dairyking98/Type-Elements/v4/site/accessories.md

---
layout: page
title: Accessories
---

Non-parametric companion parts that print alongside a machine's type
elements but aren't generated by this pipeline - no `config/`/`lib/`
counterpart, just a checked-in model plus a writeup. New accessories
land here as they're added.

- **[Mignon Index Holder](accessories/mignon_index_holder)** - holds
  the printed-out legend card alongside the printed Mignon element.
