dairyking98/Type-Elements/v4/site/assets/thumbnails/blickensderfer.png

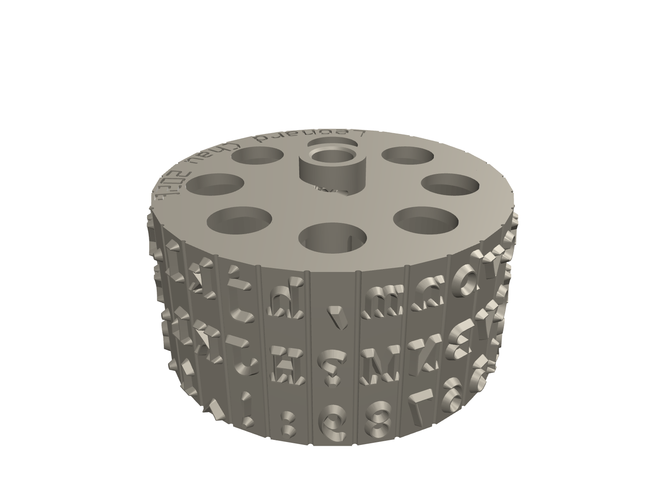
v4/site/assets/thumbnails/blickensderfer.png
