dairyking98/Type-Elements/v4/site/assets/thumbnails/glyph_A_minkowski.png

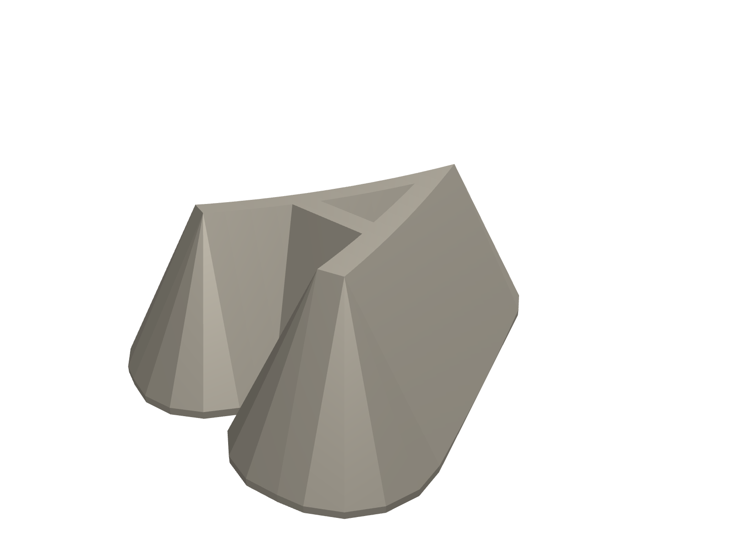
v4/site/assets/thumbnails/glyph_A_minkowski.png
