dairyking98/Type-Elements/v4/site/assets/thumbnails/glyph_A_no_minkowski.png

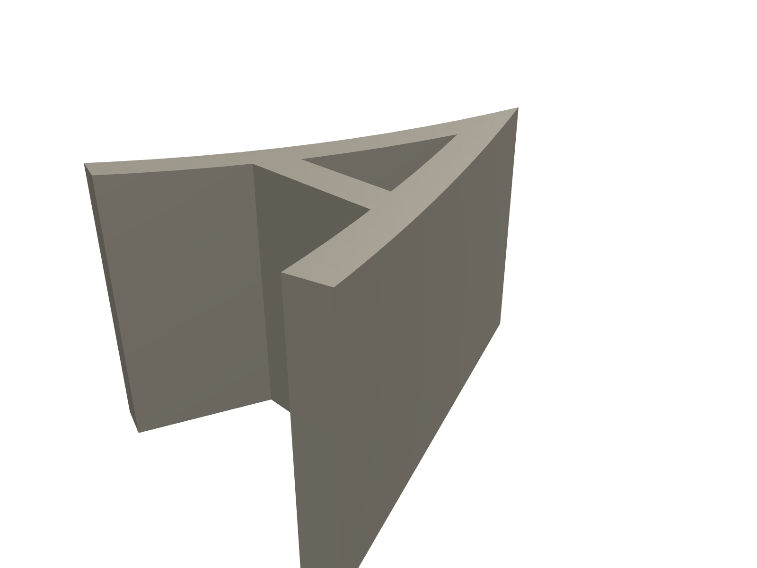
v4/site/assets/thumbnails/glyph_A_no_minkowski.png
