dairyking98/Type-Elements/v4/site/assets/thumbnails/hammond-shuttle.png

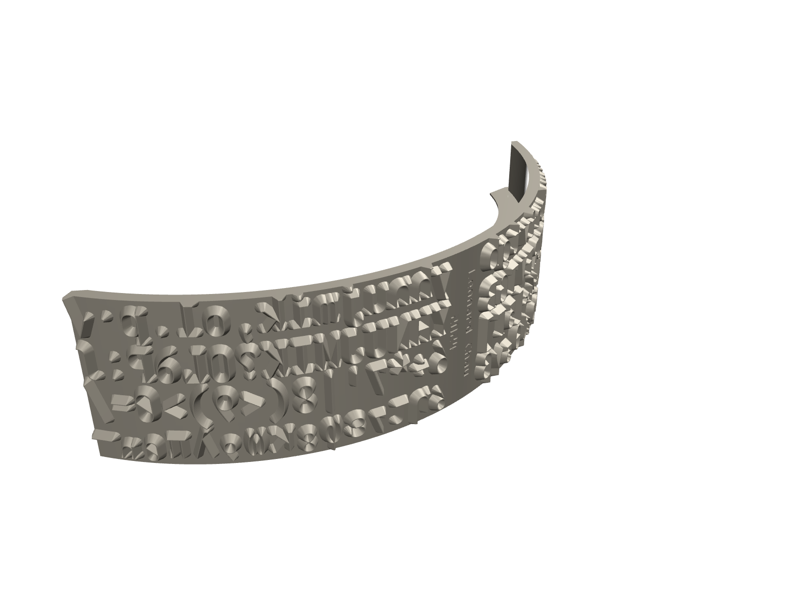
v4/site/assets/thumbnails/hammond-shuttle.png
