dairyking98/Type-Elements/v4/site/assets/thumbnails/helios-klimax.png

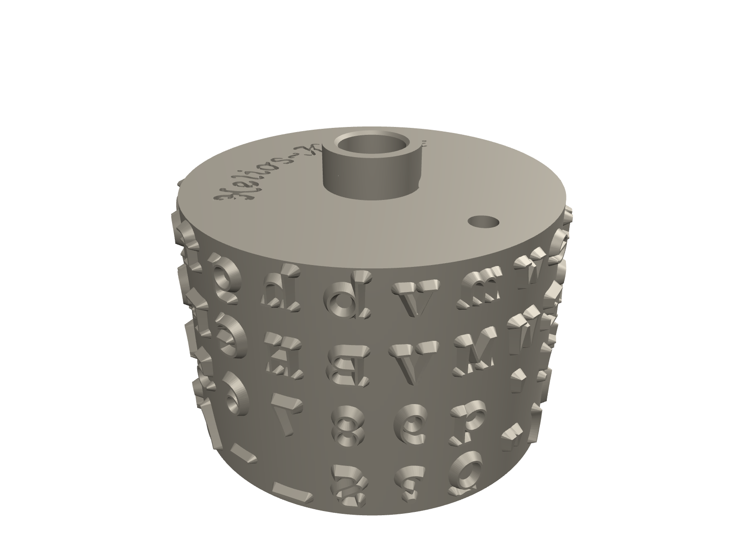
v4/site/assets/thumbnails/helios-klimax.png
