dairyking98/Type-Elements/v4/site/assets/thumbnails/mignon.png

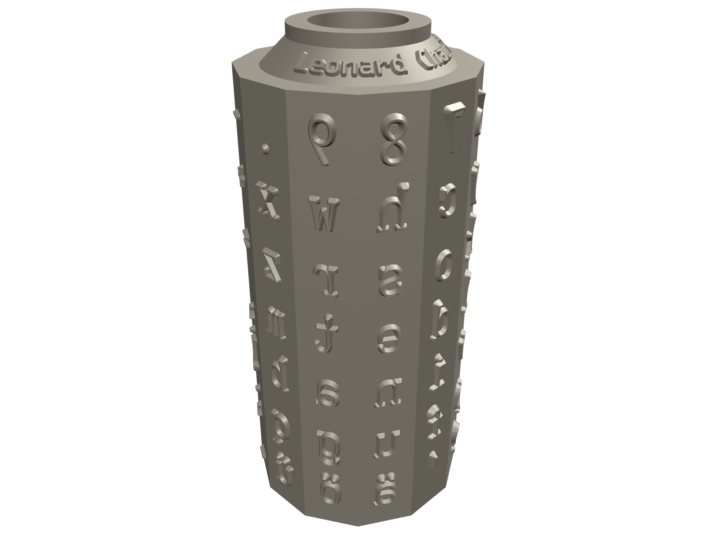
v4/site/assets/thumbnails/mignon.png
