dairyking98/Type-Elements/v4/site/assets/thumbnails/mignon_index_holder.png

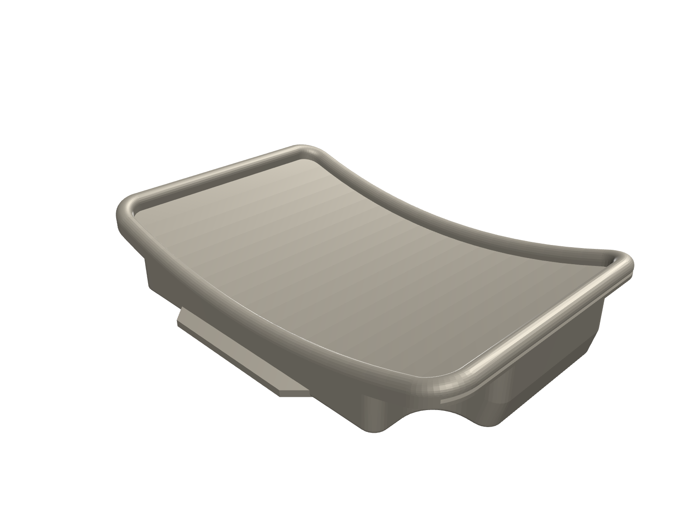
v4/site/assets/thumbnails/mignon_index_holder.png
