dairyking98/Type-Elements/v4/site/assets/thumbnails/oliver-slug.png

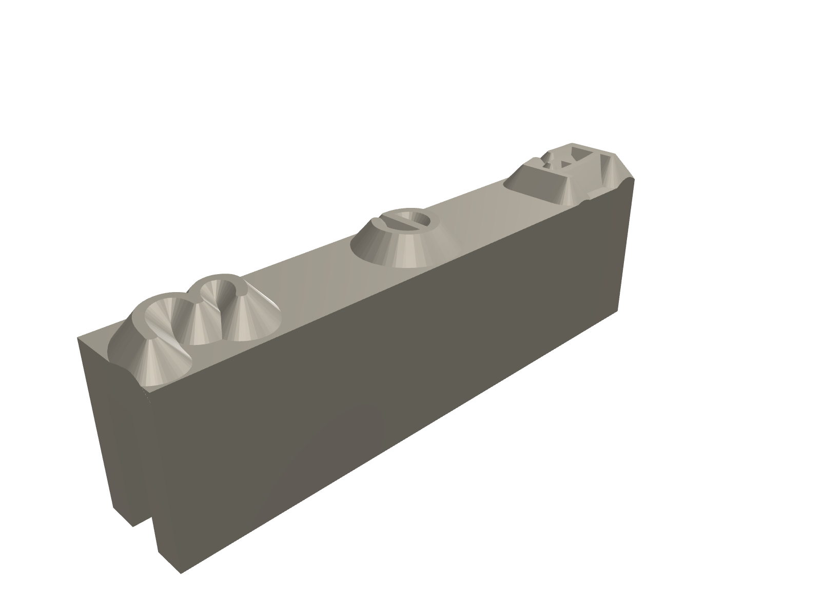
v4/site/assets/thumbnails/oliver-slug.png
