dairyking98/Type-Elements/v4/site/assets/thumbnails/postal.png

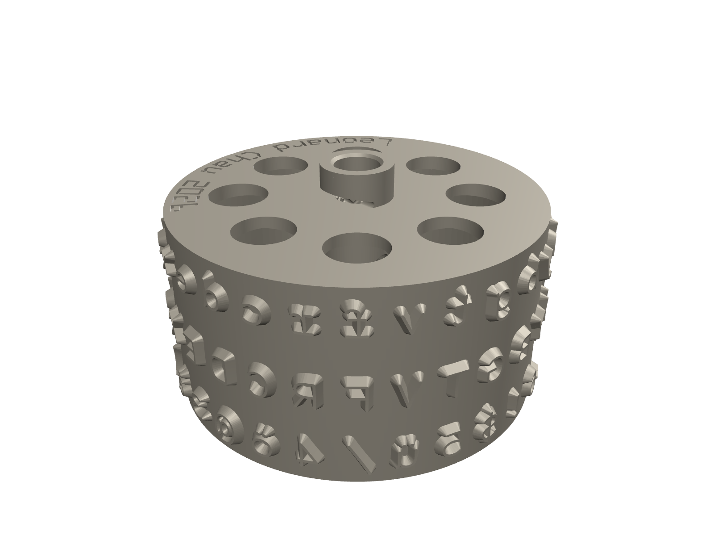
v4/site/assets/thumbnails/postal.png
