dairyking98/Type-Elements/v4/site/assets/thumbnails/resin_support_renders/blickensderfer_supports.png

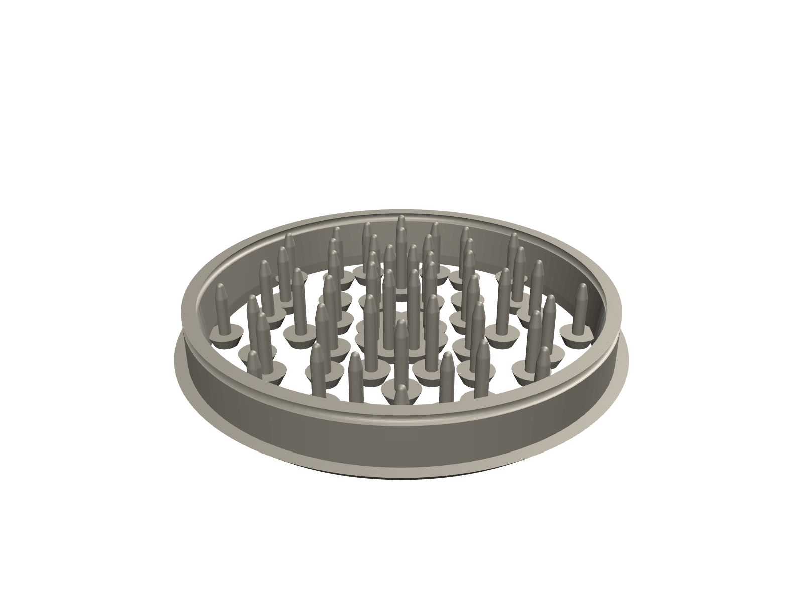
v4/site/assets/thumbnails/resin_support_renders/blickensderfer_supports.png
