dairyking98/Type-Elements/v4/site/assets/thumbnails/selectric-composer.png

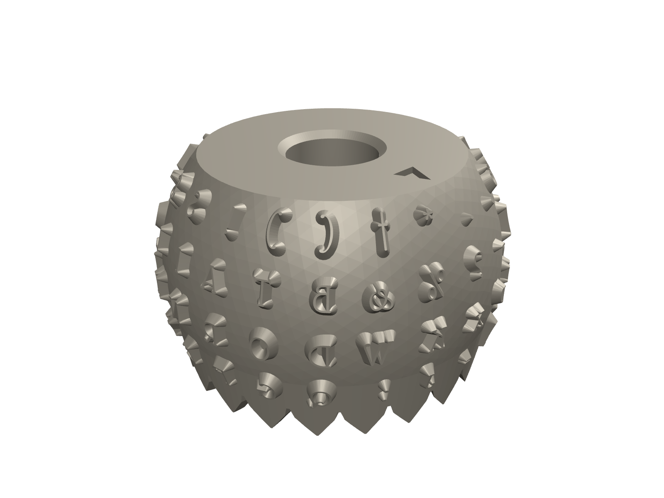
v4/site/assets/thumbnails/selectric-composer.png
