dairyking98/Type-Elements/v4/site/assets/thumbnails/type-slug.png

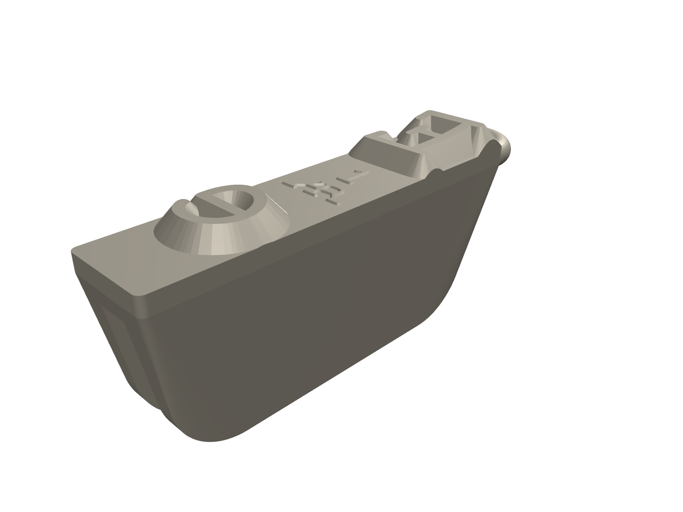
v4/site/assets/thumbnails/type-slug.png
