dairyking98/Type-Elements/v4/site/assets/thumbnails/vogue-slug.png

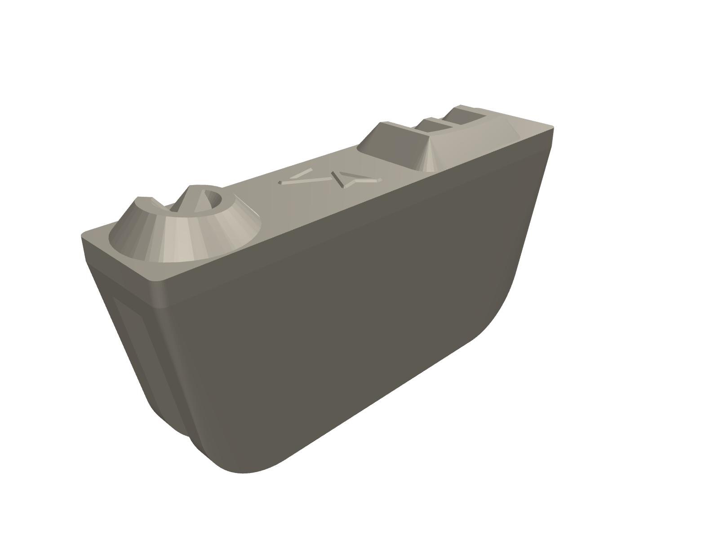
v4/site/assets/thumbnails/vogue-slug.png
