dairyking98/Type-Elements/v4/example_renders/helios-klimax.stl

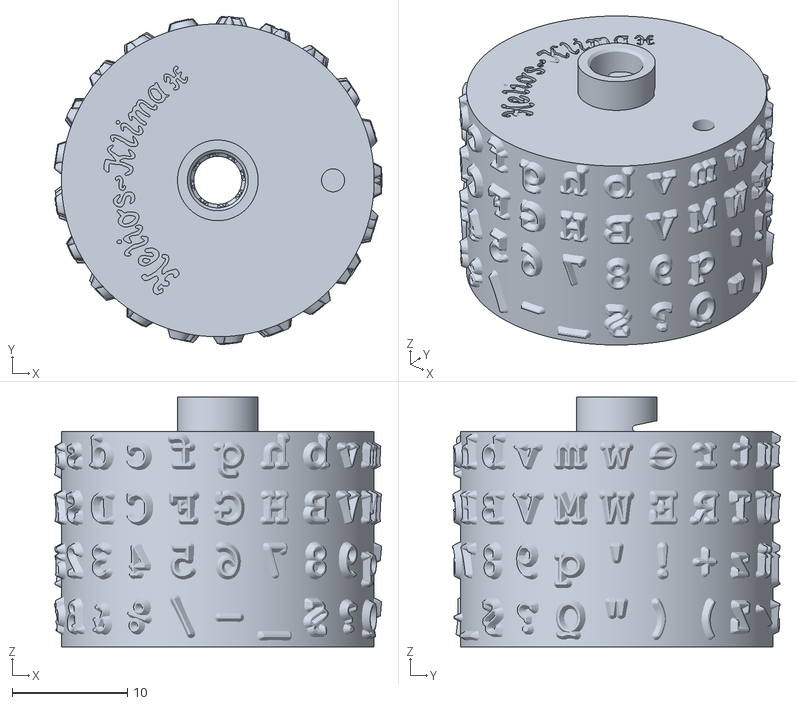
[picture p33: CAD file, 2026-08-02]
v4/example_renders/helios-klimax.stl
28.4 x 28.5 x 21.7
