dairyking98/Type-Elements/v4/example_renders/oliver-slug.stl

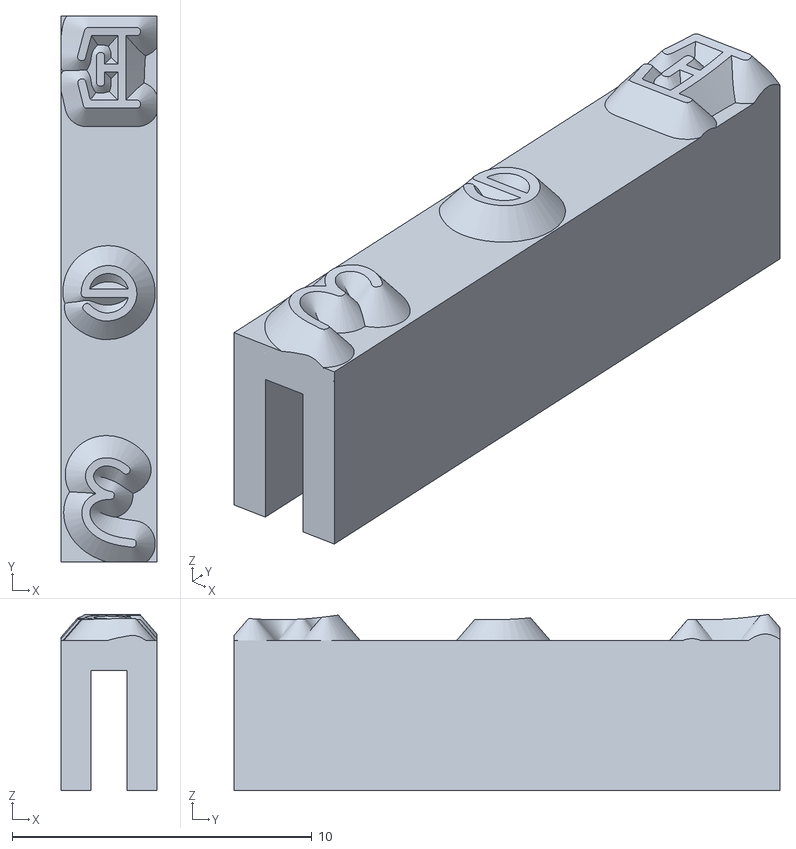
[picture p34: CAD file, 2026-08-02]
v4/example_renders/oliver-slug.stl
3.20 x 18.2 x 5.88
