dairyking98/Type-Elements/v4/example_renders/mignon.stl

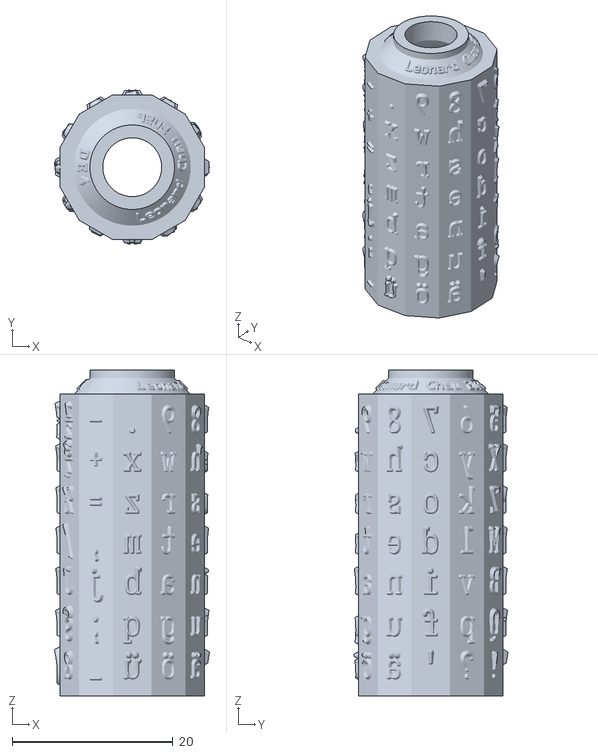
[picture p35: CAD file, 2026-08-02]
v4/example_renders/mignon.stl
19.3 x 19.2 x 40.5
