dairyking98/Type-Elements/v4/example_renders/postal.stl

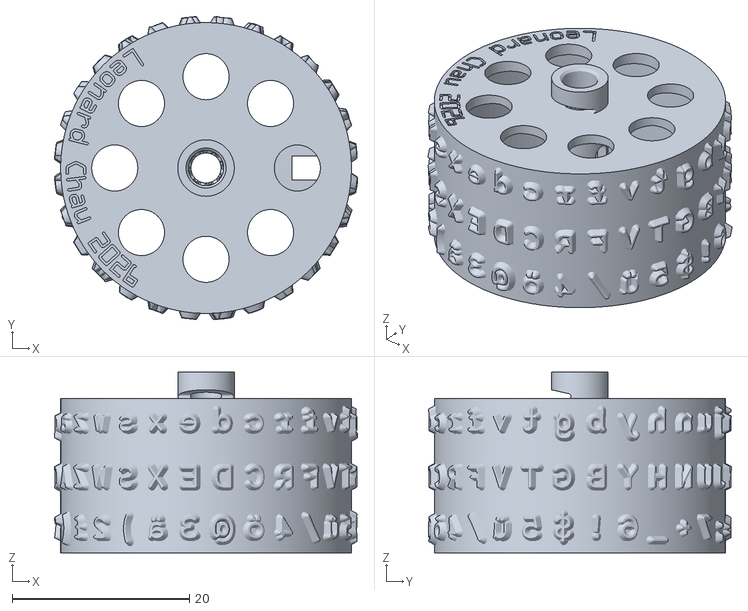
[picture p36: CAD file, 2026-08-02]
v4/example_renders/postal.stl
34.2 x 34.2 x 20.4
