dairyking98/Type-Elements/v4/example_renders/bennett.stl

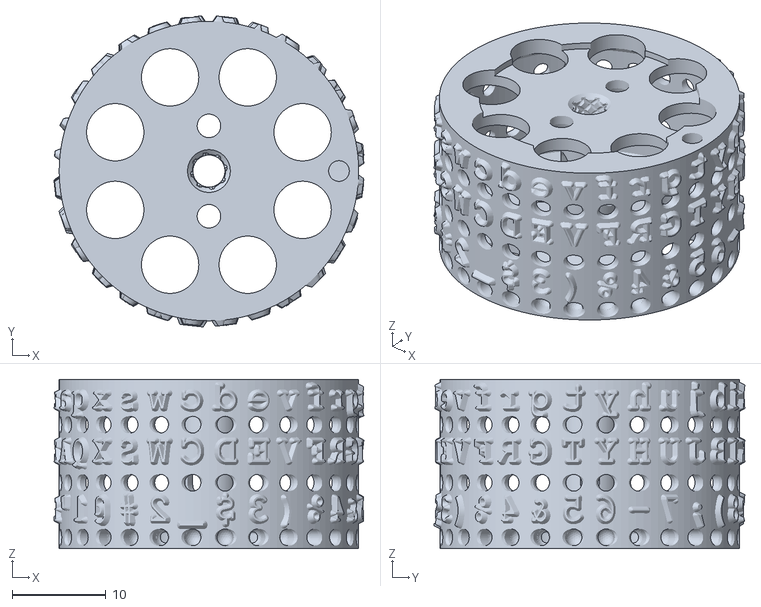
[picture p37: CAD file, 2026-08-02]
v4/example_renders/bennett.stl
33.0 x 33.1 x 18.0
