dairyking98/Type-Elements/v4/config/hammond.yaml

# Hammond type shuttle - real parameters ported from v2/hammond.scad (see
# that file's header comment for the full v2-internal glyph-pipeline
# unification derivation this config's layout/element section relies on).
#
# Hammond shares the glyph placement pipeline (place_on_cylinder/TextRing/
# CalibrationTextRing via cylinder_machine.py, plus cylinder_machine.
# _resin_rod() for the individual resin-support rod shape) with
# Blickensderfer/Postal/Mignon/Bennett/Helios, confirmed by v2/hammond.scad's
# own header comment: its arc-placement Theta formula was verified
# algebraically to reduce exactly to the shared lib's (Angle_Half_Step+
# latitude)*Latitude_Int, by treating the shuttle arc as a "fake cylinder"
# of diameter 2*Shuttle_Arc_Radius. Despite that, Hammond is NOT a
# cylinder-family body: it strikes a flat anvil (no curved platen - see
# platen_diameter below) and its body geometry (ShuttleCylinder/AnvilShape/
# Rib/PinSupport/ShuttleTaper/Label) shares nothing with cylinder_machine.py
# - see lib/hammond.py's module docstring for the full comparison.
#
# hammond_split.scad (a completely different two-piece spoke/folder
# assembly, self-contained with its own inlined glyph placement - see
# SESSION_LOG.md's Hammond audit chapter) is a SEPARATE machine in
# everything but name and is NOT covered by this config or lib/hammond.py -
# deferred to its own future port.
#
# Groove=true (v2/hammond.scad:258's alternate snap-fit/groove assembly
# variant, GroovedShuttle()/Groove()/PinSupport2()) is likewise deferred -
# Groove=false (the default) is the only variant ResinPrint's real dispatch
# path (VertResinPrint2->RibbedShuttle) exercises, so it's the one ported
# here. Cutout_Test/Cutout_Test_Array/Show_Align_Bounds (preview-only
# debug toggles, already dead/unused per v2's own comments at lines 110-113)
# are not ported, matching how other machines drop confirmed-dead v2
# customizer params.
#
# Default layout is Normal_U (LAYOUTS[0] in v2/lib/layouts/hammond_layouts.
# scad, 3 rows x 30 columns, Layout_Selection=0's default) - Hammond's other
# 7 named presets (Normal Ideal/Universal, Math/DVORAK/DHIATENSOR/Comic Mono/
# Glagolitic/Attic) are real alternate v2 presets, not yet wired into
# tune.py's named-preset picker (see SESSION_LOG.md).
#
# Typeface_2/Type_2_Size/Typeface_2_Chars (v2:167-169 - Hammond's
# always-on Glagolitic secondary-typeface tier, GalFont/GalFontSize/GalChars
# renamed) is NOT ported: it only ever matches characters that appear in
# the Glagolitic layout preset (LAYOUTS[6]), which isn't the default here -
# confirmed dead for every other layout, same treatment as bennett.yaml's
# dead-param callouts. Revisit if/when the Glagolitic preset is wired up.
# Font_Weight_Offset/X_Font_Weight_Adj/Y_Font_Weight_Adj (v2:149-151) are
# also 0/no-op in the real machine and not ported for the same reason.

machine: hammond

font:
  # v2's real value is the font family name "Iosevka Fixed Slab"
  # (Font_Size=3.10) - not installed here; nearest real file on disk.
  path: "/home/lchau/fonts/Library/Typewriter & Monospace/Iosevka Term Slab.ttf"
  size_mm: 3.10

label:
  # v2's real value is "OCR\\-A II" (a real installed font here, unlike
  # Bennett's substitution).
  font_path: "/home/lchau/fonts/Library/Typewriter & Monospace/OCR-A II Regular.ttf"
  label1: "Leonard Chau"   # Shuttle_Label1
  label2: "2024"           # Shuttle_Label2
  label_size_mm: 1.3       # Shuttle_Label_Size
  depth_mm: 0.2            # Shuttle_Label_Depth

# Real machine dimensions, v2/hammond.scad:198-262 - "shuttle" here is the
# arc-shaped print body (Anvil_OD/Shuttle_Arc_Radius is the fake-cylinder
# Element_Diameter the glyph pipeline wraps text onto; Anvil_ID is the
# printer's real anvil bore the shuttle clips around).
# Secondary font - characters listed in font2_chars are struck in this
# font/size instead of the main one. Same feature the Selectric family and
# Hammond Split have, under the same key names. Empty font2_chars =
# inactive (the default), so this changes nothing until it is filled in.
# The real use is glyph coverage: measured across the 170 distinct
# characters in all 28 Blickensderfer layout presets, Royal Vogue v3 is
# missing 87 (fractions, currency), Erica Type 52 (including "@"), Alma
# Mono and CMU Typewriter 50 each, and no non-Hebrew font covers the
# Hebrew-English preset at all.
font2:
  font2_path: ""            # blank = use the main font
  font2_size_mm: 0.0        # 0 = use the main font size
  font2_chars: ""

element:
  shrinkage_multiplier: 1.00       # Shuttle_Arc_Radius_Shrinkage_Multiplier
  anvil_od: 73.15                  # Element_Diameter = anvil_od*shrinkage_multiplier
  anvil_id_raw: 66.0
  shuttle_thickness: 1.36          # also Letter_Placement_Protrusion (v2:380)
  # v2's Shuttle_Text_Protrusion (0.9) is not carried as its own key:
  # protrusion is expressed fleet-wide as element.min_final_character_
  # diameter below, from which it is derived. Dropped rather than left as a
  # second spelling that could silently disagree.
  # Diameter across two opposing character tips - the fleet-wide way of
  # expressing protrusion (same key the cylinder machines use). The shuttle
  # surface is element_diameter + 2*shuttle_thickness = 75.87, so this is
  # 0.9mm of relief. No minimum-vs-maximum here: a flat anvil, no platen
  # scallop to vary it.
  min_final_character_diameter: 77.67
  normal_shuttle_height: 13.6
  math_shuttle_height: 18.24
  shuttle_height_offset: 3
  shuttle_rib_plane_base: 6.7      # Shuttle_Rib_Plane = this + shuttle_height_offset
  shuttle_rib_thickness: 0.24
  shuttle_rib_width: 2.9
  shuttle_square_hole_offset: 6.4
  shuttle_square_hole_width: 2.67
  shuttle_square_hole_length: 1.60
  shuttle_square_hole_radius: 0.4
  shuttle_pin_support_height: 1.5
  shuttle_pin_support_base_width: 6
  shuttle_pin_support_base_length: 7.8
  shuttle_pin_support_height_offset: 1.5
  # Shuttle_Pin_Support_Height2 (v2:236) - PinSupport2()'s own dimension
  # (that module is dead/unused - see element.groove's comment), but this
  # SAME value is also used by HorizResinSupport2's "under Pinhole" tier
  # (lib/hammond.py's HorizRibbedResinSupport()), so it's real/needed.
  shuttle_pin_support_height2: 2.0
  shuttle_rib_hump_distance: 9
  shuttle_rib_circle: 159
  shuttle_rib_circle_radius: 19
  shuttle_taper_deg: 2
  shuttle_taper_step: 0.5
  # Angle_Pitch = (angular_span_deg/angular_divisions)/shrinkage_multiplier
  # (v2:203) - the shuttle's real physical arc spans 120 degrees over 32
  # divisions; Latitude_Int (the glyph pipeline's column-to-angle step)
  # is this same value, not an independently-tunable one.
  angular_span_deg: 120
  angular_divisions: 32
  # Is_Math (v2:128 - search(LAYOUTS[Layout_Selection][3],"Math")) is
  # DERIVED in lib/hammond.py's configure() from len(layout.rows)==4 (the
  # Universal, Math preset is the only real 4-row layout - see tune.py's
  # Layout tab) - not a separate settable toggle here, so it can't drift
  # out of sync with which preset is actually selected.
  # Rib()'s fillet region insets its resin-support-clearance corner by this
  # much (v2:351 "Cp_1_X=Shuttle_Arc_Radius*cos(Theta_A)-2  //limit of resin
  # support" - a real, named machine clearance, not a construction sentinel).
  rib_fillet_resin_clearance: 2.0
  # Groove (v2:258) - the shuttle's two real, mutually-exclusive BODY
  # ASSEMBLY mechanisms: false (default) is the internal rib + square
  # drive-pin boss (Rib()/PinSupport()/PinSupportHole(), assembled
  # separately and glued/pinned to the shuttle body); true is a snap-fit
  # groove cut directly into the shell (Groove()/ResinChamfer(), no
  # separate rib piece at all) - see lib/hammond.py's GroovedShuttle()-
  # equivalent path for the full derivation. tune.py's Build tab shows
  # this as the "Rib" checkbox (inverted) - user-facing wording is
  # "Without Rib" for groove=true, to avoid confusion with the
  # UNRELATED resin.horizontal_method "Cut Groove" option below (a
  # resin-support scheme, not a body-assembly choice - the two used to
  # share the word "groove" with no way to tell them apart by name).
  # v2's PinSupport2()/Groove_Retaining_Pin_Diameter are declared but
  # never actually called/referenced anywhere in v2/hammond.scad -
  # confirmed dead code, not ported (same convention as bennett.yaml's
  # dead-param callouts).
  groove: false
  shuttle_groove_nub_angle: 29           # Shuttle_Groove_Nub_Angle (deg)
  groove_tab_width: 3.15                 # Groove_Tab_Width (3+.15 in v2)
  groove_opening_offset: 0.5             # Groove_Opening_Offset
  support_groove_thickness: 0.5          # Support_Groove_Thickness - also
                                          # derives Support_Groove_R, used by
                                          # resin.horizontal_method's Cut
                                          # Groove ring (v2:322 also uses it
                                          # for ResinChamfer(), currently
                                          # disabled - see lib/hammond.py's
                                          # Additive())
  # v4-specific, not a v2 value - FDM print-fit clearance for the "Rib"
  # Build target's groove-interface flange (RibOnly(), see its own
  # docstring and GrooveShape()'s "shrink" parameter). Shrinks the
  # flange (printed as its own separate FDM part, meant to snap into a
  # "Shuttle" (groove=true) body's cut slot) rather than growing the
  # Shuttle's own groove cut - typical FDM practice, printers tend to
  # oversize solid protrusions more than they undersize cut features.
  # 0.15mm is a reasonable starting point for a snug slide-fit at
  # typical 0.4mm-nozzle FDM tolerances - tune per printer/filament.
  rib_interface_offset_mm: 0.15
  # v4-specific, not a v2 value - extra radius added to the Rib flange's
  # 4 nub-clearance cutouts (see GrooveShape()'s nub_grow parameter),
  # independent of rib_interface_offset_mm - gives the flange's own
  # clearance holes some FDM-fit margin over the Shuttle-side nub
  # geometry. Only affects RibOnly(), never the Shuttle-side cutter.
  rib_nub_growth_mm: 0.15
  # v4-specific, not a v2 value - how far the Rib flange's center tang
  # (the feature that plugs through the Shuttle's cut opening) reaches,
  # in absolute mm from the rotation axis. Deliberately OMITTED here -
  # lib/hammond.py's configure() defaults it to Shuttle_Arc_Radius+
  # Shuttle_Thickness (the Shuttle's own real outer wall radius) when
  # this key is absent, so the tang sits flush with the Shuttle's real
  # outer surface automatically, tracking those two values instead of a
  # separately-maintained literal that could drift out of sync with
  # them. Only add this key (see lib/hammond.py's Rib_Tang_Length
  # comment) if a physical fit-check shows it should stop short of or
  # protrude past that surface.
  # rib_tang_length_mm: <override, mm from rotation axis - see comment above>
  # v4-specific, not a v2 value - RibOnly() only: when true, omits
  # PinSupport()'s "top" boss (keeps only "bottom"), so the printed part
  # has a protruding pin-boss feature on one Z side only and can sit
  # flat on the buildplate without needing supports under the other
  # side's overhang. Never applied to the fused Shuttle with Rib print.
  rib_flat_bottom: false

# quality/facet counts - v2:79-92. Surface_Fn mirrors Cyl_Fn (v2's own
# comment: "no separate structural-quality tier from Cyl_Fn").
quality:
  cyl_fn: 360
  surface_fn: 360
  minkowski_fn: 12                 # Mink_Fn
  # Wall banding. The body is pre-split into horizontal bands so the boolean
  # that unions the characters into it never has a full-height face to
  # shatter into long near-zero-area slivers. Bands are never made SHORTER
  # than this; 0 = auto, one band per angular facet width (bands roughly as
  # tall as they are wide). Raise it to coarsen an over-fine wall.
  min_band_height_mm: 0.0

# Baseline (v2:130) is [Lowercase, Uppercase, Figures, Math], measured from
# the bottom RIB plane (Baseline_Z_Offset=Rib_Bottom_Z, a derived value -
# see lib/hammond.py's configure()). This master config's default layout
# (Universal) has only 3 rows, so only the first 3 entries apply
# here - the real 4th (Math, -9.89) value lives in tune.py's
# LAYOUT_PRESET_BASELINE_ROW_BY_MACHINE["hammond"]["Universal, Math"],
# applied automatically when that layout preset is selected (switches
# baseline_row/cutout_row to 4 entries at the same time as rows, since
# Is_Math is derived from row count - see lib/hammond.py's configure()).
# Cutout (v2:133) is unused (Skip_Platen_Cutout=true, see lib/hammond.py)
# - cutout_row is set equal to baseline_row as a documented no-op rather
# than porting the dead [0,0,0,0].
#
# Placement_Map (v2:371, col<=14 ? col-16 : col-14) is Hammond's real
# non-identity physical-column mapping for the arc's seam at column 14/15 -
# materialized as literal data here (not computed from layout.rows' length
# at load time) matching how every other machine stores placement_map, per
# this repo's "pick one convention, don't let it re-fork per machine" rule
# - tune.py's Layout tab reads layout.placement_map/latitude_columns
# directly. latitude_columns must stay in sync with placement_map/rows -
# edit both together if you ever change layout.rows' column count.
layout:
  baseline_row: [3.74, -1.21, -5.71]
  # Cutout (v2:133) is unused - Skip_Platen_Cutout means the (y-offset)^2
  # scallop term is multiplied by platen_radius_mm=0 regardless of offset,
  # so cutout_row-baseline_row's value can't affect geometry. Set equal to
  # baseline_row (offset=0) as a documented no-op rather than porting the
  # dead v2 Cutout=[0,0,0,0] - stored literally (not derived at load time)
  # since tune.py's Element tab reads layout.cutout_row directly, same as
  # baseline_row.
  cutout_row: [3.74, -1.21, -5.71]
  latitude_columns: 30
  placement_map: [-16, -15, -14, -13, -12, -11, -10, -9, -8, -7, -6, -5, -4, -3, -2, 1, 2, 3, 4, 5, 6, 7, 8, 9, 10, 11, 12, 13, 14, 15]
  rows:
    - "-;p.lo,kimjunhybgtvfrcdexswzaq"
    - "!:P.LO?KIMJUNHYBGTVFRCDEXSWZAQ"
    - "/=0.)9°(8^'7*&6¢_5£%4+$3×#2@\"1"
  modify_glyphs: false

alignment:
  mode: "center"
  center_offset_mm: 0.0
  left_offset_mm: 0.0
  modified_left_chars: ""
  modified_left_offset_mm: 0.0
  modified_right_chars: ""
  modified_right_offset_mm: 0.0
  # Per-character baseline overrides, y-axis counterparts to the
  # modified_left/right_chars nudges above (see glyph_poc.alignment_offset).
  # caret_drop_mm shifts "^" DOWN - the Blickensderfer's caret sits on the
  # baseline, but digital fonts draw U+005E up at cap height because there
  # it doubles as the spacing circumflex accent. underscore_lift_mm shifts
  # "_" UP - many TTFs sink U+005F well below the baseline to clear
  # descenders in running text, which drops it out of the character cell on
  # a struck element. Both 0.0 = use the font's own glyph position, i.e. the
  # behavior every config had before these keys existed. Idea/problem
  # statement from RobertG's OpenSCAD Blickensderfer generator
  # (badonoer.blogspot.com, CC BY-SA 4.0) caretDrop/uScoreLift.
  caret_drop_mm: 0.0
  underscore_lift_mm: 0.0

# mesh-pipeline build settings (v4-specific, not real v2 numbers) - see
# config/bennett.yaml's matching comment. platen_diameter=0/no cutout
# (Skip_Platen_Cutout=true, v2:384 - Hammond strikes a flat anvil, not a
# curved platen) translates to platen_radius_mm=0 in build_glyph's
# scallop formula z=(y-offset)^2*platen_radius_mm - a real 0 makes the
# scallop term vanish for every y, i.e. a genuinely flat print face,
# rather than an undefined 1/0. See lib/hammond.py's configure().
build:
  flatness_tolerance_mm: 0.005
  pre_minkowski_char_height_mm: 1.0
  # MINKOWSKI CONE HEIGHT - the tapered part of the character, added BELOW
  # the straight part. Total character depth is pre_minkowski_char_height_mm +
  # this, and the tip does not move when either changes. Lower it for a
  # shallower flare without pulling the root out of the wall - which is
  # what shrinking the character alone used to do, until the roots lifted
  # clear and the characters floated free of the body.
  minkowski_cone_height_mm: 2.0
  # Trim each placed character to its own angular slot so its Minkowski
  # draft skirt cannot bleed into the neighbouring character. See
  # cylinder_machine._clip_to_cell. Off = the historical behavior.
  clip_to_cell: false
  resin_support: true               # Resin_Support (v2:298)
  target: "element"
  minkowski_enabled: false           # Mink_On default (v2:102)
  draft_angle_deg: 55.0              # Mink_Draft_Angle (v2:106)

# Resin support: individual rod SHAPE reuses cylinder_machine._resin_rod()
# (same shared primitive Mignon/Bennett already reuse - NOT Hammond's own
# v2 ResinRod()/RodTip() modules, which are custom one-off variants of the
# same idea). Placement is Hammond-specific (lib/hammond.py) since the
# arc-shaped body has no radial-wall/sloped-core topology for cylinder_
# machine.py's BottomSupports/SpeedHoleSupport/DrivePinSupport placement
# layer to apply to - v2/lib/resin_support.scad's own header explicitly
# excludes Hammond/IBM from that placement layer for this reason. The one
# genuinely new primitive is the angled reinforcement rod between adjacent
# support rods (gusseting) - sp.connecting_rod(), ported from v2's
# ConnectingRod() (v2/hammond.scad:419), which doesn't exist for any other
# machine since none of their resin-support systems brace rods against
# each other.
resin:
  resin_fn: 20
  rod_od: 0.9                       # Resin_Support_Rod_Thickness
  tip_od: 0.4                       # Resin_Support_Contact_Diameter
  tip_l: 1.0                        # RodTip()'s h=1 cylinder section
  inset: 0.2                        # tip_od/2, same convention as bennett.yaml
  min_rod_height: 2.0                # Resin_Support_Min_Height
  raft_thickness: 1.5                # Resin_Support_Base_Thickness
  raft_od: 1.6                       # 2*Resin_Support_Buildplate_Radius
  spacing: 3.0                      # Resin_Support_Spacing - real angular
                                     # rod pitch is spacing/Shuttle_Arc_Radius
                                     # radians (v2:615's thetaspacing formula)
  edge_gap: 0.1                     # Resin_Support_Edge_Gap (v2:314)
  tip_interference: 1.2             # Tip_Interference (v2:324) - ResinRod2()'s
                                     # real tip overlap-fit depth (horizontal,
                                     # non-grooved support only). NOT currently
                                     # consulted by lib/hammond.py's _rod2() -
                                     # v2's real value was calibrated against
                                     # ResinRod2's own hardcoded 2mm cone, which
                                     # doesn't match this port's substituted
                                     # resin_rod() shape (Resin_Tip_L=1.0mm) -
                                     # see _rod2()'s docstring. Kept as real,
                                     # documented v2 machine data, not deleted.
  # Resin_Support_Orientation (v2:300) - "vertical" stands the shuttle up
  # on one end (v2's VertResinPrint2, rotate([0,-90,0])) and reuses v2's
  # real VertResinSupport2() placement math (lib/hammond.py's
  # ResinSupport()). "horizontal" prints it flat in its natural as-built
  # frame, outer-wall support scheme picked by horizontal_method below.
  orientation: vertical              # [vertical, horizontal]
  # horizontal_method - v4-specific, NOT a direct v2 customizer field
  # (v2:1060-1073's real ResinPrint() dispatcher only ever wires up
  # HorizGroovedResin3 for Resin_Support_Orientation==1 - HorizResinPrint2/
  # HorizResinSupport2, the rod scheme, are real complete v2 functions but
  # never called from there; see lib/hammond.py's ResinPrint() docstring
  # for the full derivation of why both are ported and exposed anyway).
  # Picks which OUTER-WALL horizontal support scheme is used, independent
  # of element.groove/the Build tab's Rib checkbox: "cut_groove" is
  # HorizGroovedResin3's swept perforated breakaway-groove ring
  # (HorizGroovedResinSupport()); "resin_rod" is HorizResinPrint2/
  # HorizResinSupport2's real per-rod scheme for the outer wall
  # (HorizWallRodSupport()). v2:1006-1021/864-950 respectively - both
  # real, faithfully-ported v2 schemes, not a simplified stand-in.
  # Independent of body assembly because the ring only spans the outer
  # wall band (r0..r0+Shuttle_Thickness) and never touches the rib
  # feature either way - but whenever the body actually HAS a rib
  # (element.groove=false), the rib's own back-plane/pin-hole area still
  # always needs its own resin-rod supports regardless of this setting
  # (HorizRibResinSupport() - there's no cut-groove equivalent for that
  # geometry), added on top of whichever outer-wall method is chosen here.
  horizontal_method: resin_rod       # [cut_groove, resin_rod]

output:
  directory: "output"
  stl_name: "hammond_running.stl"

# tune.py's Type Test tab (v4-specific) - see config/bennett.yaml's
# matching comment.
type_test:
  cpi: 10.0                         # Test_CPI
  lpi: 6.0
  text: |-
    The quick brown fox jumps over the lazy dog 1234567890

# Calibration - v2 has no Cutout_Test/Baseline_Test defaults active
# (Cutout_Test=false at v2:110, Baseline_Test=false at v2:115), same as
# Bennett's real defaults.
calibration:
  test_char: "H"
  vary_baseline: false
  vary_cutout: false
  start: -0.7
  interval: 0.05

# The flat 2D "index" reference card - v1/Hammond/HammondIndex.scad
# ported to lib/hammond_legend.py (SVG output via generate_legend.py,
# entirely separate from the 3D element build above - see that module's
# docstring). Every number below is v1's real customizer default
# (HammondIndex.scad line cited), not invented. Displays layout.rows
# above as a conventional QWERTY-style 3-row x 10-column reference,
# reading the real 30-key shuttle arc.
legend:
  # Real per-row hand-measured spans against an actual original card
  # (2026-08-06), replacing v1's own taper-formula-derived approximation
  # (v1 QP_Length=178/ZExclamation_Length=200.4, no separate A-to-:
  # measurement at all - see lib/hammond_legend.py module docstring's
  # divergence note). qp_length_mm's value happens to be unchanged from
  # v1's own (178.0mm) - real coincidence, not copied verbatim.
  qp_length_mm: 178.0                 # Q key to P key, top row
  a_colon_length_mm: 188.0            # A key to : key, middle row
  z_exclamation_length_mm: 198.0      # Z key to ! key, bottom row
  # Row-to-row vertical pitch (both Q<->A and A<->Z gaps) and the
  # absolute anchors - see lib/hammond_legend.py's _locate() docstring.
  row_separation_mm: 18.45
  left_margin_mm: 38.0                # shared start x for all 3 rows (Q/A/Z vertically aligned)
  bottom_margin_mm: 9.2                # card bottom edge to the Z row
  # Real fixed cut size - not derived from content bounds (this card's
  # margins are genuinely asymmetric top/bottom). Width = left_margin_mm
  # + z_exclamation_length_mm (the widest row) + a matching 38mm right
  # margin = 274.0mm exactly.
  card_width_mm: 274.0
  card_height_mm: 60.0
  card_corner_radius_mm: 19.0         # top two corners only - see _card_border()
  # The rounding circle's own center height (not derived as card_height_mm
  # - card_corner_radius_mm - a real independent measurement). 38+19=57mm
  # falls short of card_height_mm (60mm), so the arc needs a straight
  # vertical bridge up to the top edge - see _card_border()'s docstring.
  card_corner_center_y_mm: 38.0
  card_border_stroke_mm: 0.1          # SVG stroke width for the cut-outline path (visual only, not a cut parameter)
  circle_id_mm: 14.0                  # v1 Circle_ID (:60)
  circle_thickness_mm: 0.5            # v1 Circle_Thickness (:61)
  cap_size_mm: 6.0                    # v1 CAP_Size (:54)
  fig_size_mm: 4.0                    # v1 FIG_Size (:56) - also reused for the lowercase/punctuation label (v1 does the same, :135/181)
  capfig_mod_size_mm: 4.0             # v1 CAPFIG_ModSize (:58)
  fig_offset_mm: 2.5                  # v1 FIG_Offset (:40)
  lowercase_offset_mm: -5.5           # v1 Lowercase_Offset (:42)
  cap_offset_mm: -4.5                 # v1 CAP_Offset (:44)
  fig_dupe_offset_mm: 3.0             # v1 FIG_Dupe_Offset (:46)
  capfig_offset_mm: -1.5              # v1 CAPFIG_Offset (:48)
  capfig_mod_chars: "!:?-\"&"         # v1 CAPFIG_Mod (:21)
  # v1 Lowercase_Mod (:23) - minus the literal "☺" (a real character in
  # v1's string, but not a meaningful key on any of this config's real
  # layout.rows), PLUS "-" - v1's own real Layout[0][0]="-" (a genuine
  # standalone character, not the lowercase form of its own key's CAP
  # letter, "!") is missing from v1's own Lowercase_Mod (confirmed: a
  # real openscad-nightly render of the actual v1 file shows the same
  # gap - no dash anywhere), so the dash never gets drawn in v1's real
  # output either. Added here as a deliberate fix rather than
  # reproducing that gap - a legend that silently drops a real character
  # is a real usability bug regardless of source fidelity.
  lowercase_mod_chars: ";,'-"
  fig_dupe_chars: "."                 # v1 FIG_Dupe (:25)
  circle_segments: 32                 # v4-only - shapely buffer() quad_segs for every circle (v1 used OpenSCAD's default $fn)
  legend_flatness_tolerance_mm: 0.01         # adaptive glyph-outline tolerance (see glyph_poc.py) - a paper legend needs far less precision than a struck element
  # v4-only, not a v1 concept - SVG canvas background: "transparent"
  # (default, no backing rect) or "white" (an opaque backing rect).
  background: "transparent"
  # v4-only, independent of font.path above - see config/mignon.yaml's
  # matching legend.legend_font_path comment (both the "why a separate
  # font" and the "why legend_font_path not bare font_path" reasoning -
  # this config's own label.font_path already owns that key text). v1's
  # real value is the font family name "Franklin Gothic" (HammondIndex.
  # scad's Legend_Font) - now installed here.
  legend_font_path: "/home/lchau/fonts/Library/Sans Text/Franklin Gothic.ttf"
