dairyking98/Type-Elements/v4/config/hammond_split.yaml

# Split Hammond 1 Shuttle - real parameters ported from v2/hammond_split.scad
# (771 lines, "HammondSplitShuttle2.scad" pre-migration). This is a SEPARATE
# machine from Hammond (config/hammond.yaml/lib/hammond.py) in everything but
# name - see SESSION_LOG.md's Hammond audit chapter (part 29) and
# v2/hammond_split.scad's own header comment: hammond_split.scad has ZERO
# include statements (fully self-contained), builds its own inlined
# TextAssemble/TextPlacement/LetterText/TextRing(side) glyph pipeline (NOT
# wired to v2/lib/glyph_pipeline.scad, and NOT reusing v4's
# cylinder_machine.place_on_cylinder/TextRing the way lib/hammond.py does),
# and its own header calls this file "closer to IBM's spherical geometry"
# than the cylinder family. It's a two-piece spoke/folder assembly (Arc/
# Spoke*/Tube/FolderClearance/GlueHoles) with a third independent
# resin-support scheme (not v2/hammond.scad's VertResinSupport2, not any
# cylinder-family scheme) - see lib/hammond_split.py's module docstring.
#
# Two physically separate printed halves (Left=side0/Right=side1), each a
# mirror image of the other about the Y=0 plane (v2's Mirror(side) -
# lib/scad_primitives.mirror()) apart from the struck glyph text, which is
# independently placed per side (TextAssemble(side)'s own per-side angle-
# sign/character-index formula - not just a mirror of the same text). Both
# halves ship in ONE STL as physically separate (non-overlapping,
# print-oriented) solids - see ResinPrint()/FullElement()/NormalElement()'s
# docstrings.
#
# TWO real, complete render targets exist in the source, not one -
# v2/hammond_split.scad:60's own customizer comment names them directly:
# `Render_Mode=1;//[0:Normal, 1:ResinPrint, 2:Type Test]`, and v1's pre-
# migration original (v1/Hammond/HammondSplitShuttle.scad:16) is even more
# explicit: `GenStyle = 1; //[0:Normal, 1:ResinPrint, 2:ResinPrintL,
# 3:ResinPrintR, 4:NormalL, 5:NormalR]`. "ResinPrint" (Render_Mode==1/
# GenStyle 1-3) is the vertical, tipped-up, resin-supported layout
# (ResinPrint()/FullElement(), the only one wired up in the original port
# session) - "Normal" (Render_Mode==0/GenStyle 0/4/5) is a flat, un-rotated,
# UNCONDITIONALLY resin-free layout (NormalElement(), wired up in a later
# session once this doc header itself led someone to re-check v1 closely
# and find it) - neither is "more real" than the other, both exist in every
# version of this machine's source that's ever been found.

machine: hammond_split

font:
  # v2's real value is the font family name "Average Mono" - actually
  # installed on disk here (unlike hammond.yaml's Iosevka substitution).
  path: "/home/lchau/fonts/Library/Typewriter & Monospace/AverageMono.otf"
  size_mm: 2.95                    # Type_Size

# Char_Mod ("⅌", the per-unit sign) uses a separate font/size from every
# other character - v2:94-99. v4 has no per-character font override in the
# shared glyph pipeline (this file builds its own from scratch - see
# lib/hammond_split.py's LetterText()), so this is read directly by
# TextAssemble()'s own per-character font/size choice.
font2:
  font2_chars: "⅌"                        # Char_Mod
  # Renamed from the bare "font_path"/"size_mm" every other section uses -
  # tune.py's patch_yaml_value() searches for a FIELDS key's literal text
  # anywhere in the file (not scoped by section), so a leaf name shared
  # with font.path/label.font_path or font.size_mm would silently patch
  # whichever occurrence comes first in the file instead of this one.
  font2_path: "/home/lchau/fonts/Library/Typewriter & Monospace/Noto Sans Mono.ttf"
  font2_size_mm: 2.7            # Char_Mod_Size

label:
  # Logo (v2:169-180) - engraved surface label, read directly (never
  # struck) - same convention as every other machine's Logo/Label text.
  font_path: "/home/lchau/fonts/Library/Typewriter & Monospace/OCR-A II Regular.ttf"
  label1: "Leonard Chau"           # Logo_Text_1
  label2: "2025"                   # Logo_Text_2
  label_size_mm: 1.9               # Logo_Size
  depth_mm: 0.3                    # Logo_Depth
  # Radial distance (mm, from the hub axis) both label lines are
  # halign=center-anchored on, along the first inner spoke's own
  # centerline - v2/v1's literal translate([16,...]) in Logo() (v2:479).
  # v4 fixed Logo()'s angle to actually track a real spoke (see
  # lib/hammond_split.py's Logo() docstring - v2/v1's own folderArcStart
  # placement didn't track any real spoke and left the label cutting into
  # open air past the center hub) - this radial anchor stays independently
  # tunable since the usable span differs per spoke/config (currently
  # ~0mm-35.9mm = Arc_OD/2-Arc_Thickness for the master config).
  radial_offset_mm: 22.5           # Logo_Radial_Offset

# Key Mapping (v2:75-87) - Ideal_Element (Layout_Selection=0, the real v2
# default) is the only layout ported; Qwerty_Element (Layout_Selection=1)
# is a real, complete alternate v2 preset not yet wired into tune.py's
# named-layout picker (same deferred-preset treatment as hammond.yaml's
# other 7 unwired presets - see that config's header comment).
layout:
  # NOTE: 'b', not 'd', at index 7 (and 'B' at index 7 of the caps row).
  # v1/v2 both read "...jgdmpcfld..." here (v1/Hammond/
  # HammondSplitShuttle.scad:24, v2/hammond_split.scad:76) - that is a
  # transcription error in the ORIGINAL source, not a v4 porting slip: it
  # drops 'b' from the layout entirely and repeats 'd' twice, which no
  # English typewriter does. Corrected against the primary source (the
  # Hammond Typewriter Company's own "ENGLISH Type Shuttles" catalog, Form
  # QQ-10M-11-20-W, Nov 1920), whose Ideal entries all read
  # "?zxqkjgbmpcfld," / "!ZXQKJGBMPCFLD;". This is the one case CLAUDE.md's
  # "v2 is ground truth" rule defers - the catalog is what v2 was itself
  # transcribed from.
  rows:
    - "?zxqkjgbmpcfld,.taherisounwyv:"
    - "!ZXQKJGBMPCFLD;-TAHERISOUNWYV&"
    - "¾%⅞⅝½⅜1⅛2¢3£4$56“7”8’9[0]¼*⅓†⅔"
  # Baselines[row] (v2:103-107 - Baseline_Gaps[row]+Baseline_Offset,
  # measured from the shared folder center plane, Folder_Thickness/2 - see
  # TextPlacement()), stored as the final absolute per-row value directly -
  # matching every other machine's layout.baseline_row convention (real
  # values here: [9.45,4.725,0.0] + (-1.9) = [7.55,2.825,-1.9]) - rather
  # than storing Baseline_Gaps/Baseline_Offset as separate live keys, per
  # this repo's "pick one convention" rule.
  baseline_row: [7.55, 2.825, -1.9]
  # No curved-platen/cutout concept anywhere in this machine's real
  # geometry (TextRing() trims via a real Arc intersection instead - see
  # lib/hammond_split.py's module docstring) - set equal to baseline_row
  # as a documented no-op, same convention as hammond.yaml's own unused
  # Cutout_Row for the same underlying reason (no curved platen).
  cutout_row: [7.55, 2.825, -1.9]
  # placement_map/latitude_columns - length-only, no indirection meaning
  # for this machine (TextAssemble(side)'s own char=Layout[baseline][14-i]/
  # [29-i] formula addresses Layout directly, no physical-column remap) -
  # kept as literal dummy data purely because tune.py's Layout tab reads
  # layout.placement_map/latitude_columns unconditionally for every
  # machine (char_cap = len(placement_map) - see tune.py's
  # _compose_layout_tab), same "dead but required for the TUI" treatment
  # as Hammond's own real Cutout_Row.
  placement_map: [0, 1, 2, 3, 4, 5, 6, 7, 8, 9, 10, 11, 12, 13, 14, 15, 16, 17, 18, 19, 20, 21, 22, 23, 24, 25, 26, 27, 28, 29]
  latitude_columns: 30
  modify_glyphs: false

alignment:
  # v2/hammond_split.scad's real Text() module is a plain
  # halign="center"/valign="baseline" text() call with no per-character
  # nudge system at all (unlike the shared cylinder-family glyph pipeline
  # this machine does NOT reuse - see lib/hammond_split.py's module
  # docstring) - mode="center" with all offsets at 0 reproduces that
  # exactly. Exposed anyway (wired into LetterText() via align_kwargs)
  # since every other machine's Font & Alignment tab already expects this
  # section to exist and be live, not just a documented no-op.
  mode: "center"
  center_offset_mm: 0.0
  left_offset_mm: 0.0
  modified_left_chars: ""
  modified_left_offset_mm: 0.0
  modified_right_chars: ""
  modified_right_offset_mm: 0.0
  # Per-character baseline overrides, y-axis counterparts to the
  # modified_left/right_chars nudges above (see glyph_poc.alignment_offset).
  # caret_drop_mm shifts "^" DOWN - the Blickensderfer's caret sits on the
  # baseline, but digital fonts draw U+005E up at cap height because there
  # it doubles as the spacing circumflex accent. underscore_lift_mm shifts
  # "_" UP - many TTFs sink U+005F well below the baseline to clear
  # descenders in running text, which drops it out of the character cell on
  # a struck element. Both 0.0 = use the font's own glyph position, i.e. the
  # behavior every config had before these keys existed. Idea/problem
  # statement from RobertG's OpenSCAD Blickensderfer generator
  # (badonoer.blogspot.com, CC BY-SA 4.0) caretDrop/uScoreLift.
  caret_drop_mm: 0.0
  underscore_lift_mm: 0.0

# Element Dimensions - v2:101-167.
element:
  pin_id_mm: 1.92
  pin_radial: 7.95
  pin_theta: [68.2683, 109.968]
  pin_id_chamfer: 0.25
  tube_od_mm: [6.6548, 5.842]      # [left, right]
  tube_chamfer: 0.5
  arc_od: 75.0
  arc_thickness: 1.6
  # Diameter across two opposing character tips - the fleet-wide way of
  # expressing protrusion. The arc's outer surface is arc_od = 75.0, so this
  # is 0.8mm of relief. v2 had no such value: it hid the protrusion in
  # TextPlacement's literal 'Arc_OD/2 - 1.0', which tied it to the glyph
  # extrusion depth. No minimum-vs-maximum here - flat anvil, no scallop.
  min_final_character_diameter: 76.6
  arc_height: 13.26
  arc_height_offset: -2.62
  folder_degree_offset: 8.3
  folder_degrees: 115.8
  folder_id_mm: 12.0
  folder_od: 21.0
  folder_thickness: 9.525
  folder_close_gap: 6.0
  folder_glue_hole_id_mm: 1.15
  folder_glue_groove_r: 0.8
  folder_glue_groove_depth: 0.2
  # v2's Glyph_Height (0.8) is not carried as its own key: its only role was
  # the glyph extrusion depth, expressed here as build.pre_minkowski_char_
  # height_mm (v2's Glyph_Height + 1 = 1.8). Dropped rather than left as a
  # second, dead spelling of the same dimension.
  finger_thickness: 1.8
  spoke_thickness: 2.2
  spoke_height: 8.3
  spoke_count: 5
  spoke_extent: 45.0
  spoke_chamfer: 1.5
  rib_od: 46.8
  rib_thickness: 2.6
  rib_radius: 1.0
  # Char_Theta = 360/angular_divisions (v2:167's literal 360/96 - the full
  # circle's real physical character-slot pitch; NOT the same concept as
  # hammond.yaml's angular_span_deg/angular_divisions, which spans a
  # PARTIAL arc - this one spans the full 360deg).
  angular_divisions: 96
  # Resin Offsets - v2:186-200 (FDM/resin print-fit clearances, not
  # structural dimensions).
  id_offset: 0.13                  # Tube_OD/Pin_ID growth
  folder_radial_gap: 0.4           # Folder_ID[0]/[1] +/- split
  folder_squash_clearance: 0.3     # Folder_Half_Thickness/Tube() split

# Logo (v2:169-180) - see label: above for the real font/text/size/depth.
# Logo=true is v2's only real default (Logo=false is dead/never used) - no
# config toggle here, matching how other machines treat an always-on v2
# default (see hammond.yaml's own precedent-setting comments).

# Type Test (v2:747-762, this file's own inlined flat-layout preview -
# unlike TextAssemble's split left/right halves, a single flat 30-char/row
# array) - see config/hammond.yaml's matching comment for the shared
# tune.py Type Test tab convention.
type_test:
  cpi: 10.0                        # Test_CPI
  lpi: 6.0
  text: |-
    The quick brown fox jumps over the lazy dog 1234567890

# quality/facet counts - v2:47-54. Resin_Fn lives under resin.resin_fn
# below, not here - matches the majority convention (Blickensderfer/
# Postal/Bennett/Hammond all use resin.resin_fn; only Mignon is the
# documented quality.resin_fn outlier) per this repo's "pick one
# convention, don't add a fifth variant" rule.
quality:
  cyl_fn: 120                      # Cyl_Fn
  minkowski_fn: 20                 # Mink_Fn - renamed from mink_fn to match every other machine's key name
  # Wall banding. The body is pre-split into horizontal bands so the boolean
  # that unions the characters into it never has a full-height face to
  # shatter into long near-zero-area slivers. Bands are never made SHORTER
  # than this; 0 = auto, one band per angular facet width (bands roughly as
  # tall as they are wide). Raise it to coarsen an over-fine wall.
  min_band_height_mm: 0.0

# mesh-pipeline build settings (v4-specific, not real v2 numbers) - see
# config/hammond.yaml's matching comment. flatness_tolerance_mm feeds
# the freetype contour extraction reused for LetterText() (see
# lib/hammond_split.py's module docstring on why build_glyph() is reused for
# the Mink_On=false path but NOT for Mink_On=true).
build:
  flatness_tolerance_mm: 0.005
  # Trim each placed character to its own angular slot so its Minkowski
  # draft skirt cannot bleed into the neighbouring character. See
  # cylinder_machine._clip_to_cell. Off = the historical behavior.
  clip_to_cell: false
  render_left: true                # Render_Left
  render_right: true                # Render_Right
  resin_support: false
  # target - tune.py Build-tab UI state only (element/calibration/normal),
  # same convention as every other machine's build.target - not read by
  # lib/hammond_split.py itself (generate.py's --calibrate/--hammond-split-
  # normal flags drive CalibrationElement()/NormalElement() directly, same
  # as every other machine's own alternate-target flags). "normal" is this
  # machine's real second v2 render target (Render_Mode==0 "Normal", v1
  # GenStyle 0/4/5) - see this file's own header comment.
  target: "normal"
  # Mink_On/Mink_Draft_Angle/Mink_Height - v2:65-73. Mink_Radius is derived
  # (tan(Mink_Draft_Angle/2)*Mink_Height) in lib/hammond_split.py's
  # configure(), not stored here. Mink_Height/Mink_Radius have NO equivalent
  # in v4's shared build_glyph()/build_flat_text_drafted() convention (both
  # tie their draft cone's height to the extrusion depth itself) - v2's real
  # construction here is a cone with an INDEPENDENT fixed height (2mm) far
  # taller than Glyph_Height (0.8mm), so this machine gets its own small
  # from-scratch Minkowski helper rather than reusing either shared
  # function directly - see lib/hammond_split.py's _letter_text_drafted().
  minkowski_enabled: false          # Mink_On default (v2:66)
  draft_angle_deg: 60.0             # Mink_Draft_Angle
  # v4 convention, shared with every other machine: the glyph's own
  # extrusion depth. Replaces this machine's implicit Glyph_Height + 1.
  # NOTE its cone still differs from the cylinder family's - v2 trims
  # everything below z=0 after the sum (see _letter_text_drafted), so the
  # cone shapes a flare WITHIN this depth rather than adding depth below it.
  pre_minkowski_char_height_mm: 1.0
  minkowski_cone_height_mm: 2.0

# Resin Supports - v2:202-216 (rod shape - reuses resin_support.resin_rod/
# rod_tip, same primitives Hammond's own ResinSupport() reuses) plus
# v2:226-265 (the tiered Arc/Folder/Ring placement grid - Hammond-split-only,
# see lib/hammond_split.py's ResinSupports() docstring) plus v2:673-685's
# diagonal cross-bracing "fence" lattice (connecting_rod-based, unique to
# this machine - no other machine's resin-support system braces rods
# against each other in a full lattice, only Hammond's own single-purpose
# ConnectingRod gusset comes close).
resin:
  resin_fn: 20                      # Resin_Fn
  rod_od: 0.8                       # Resin_Rod_OD
  tip_od: 0.4                       # Resin_Tip_OD
  tip_l: 1.0                        # Resin_Tip_L
  inset: 0.3                        # Resin_Inset
  min_rod_height: 2.0                # Resin_Min_Rod_Height
  raft_od: 4.0                       # Resin_Raft_OD
  raft_thickness: 2.0                # Resin_Raft_Thickness
  # Res_Spacing/Res_Angle (v2:232-233) - the diagonal fence lattice's own
  # rod pitch/angle, independent of the tiered grid's own Res_*_Div counts
  # below (those are fixed structural divisions, not spacing-driven).
  fence_spacing: 6.0                 # Res_Spacing
  fence_angle_deg: 45.0              # Res_Angle
  # Res_Arc_Div/Res_Folder_Div/Res_Folder_Face_Div/Res_Ring_Div/
  # Res_Ring_Start_End (v2:238-245) - fixed grid-division counts for each
  # support tier, real v2 data (not construction sentinels), kept literal
  # rather than derived from spacing.
  arc_div: [15, 4]
  folder_div: [12, 2]
  folder_face_div: [3, 4]
  ring_div: [8, 3]
  ring_start_end_deg: [-45.0, 45.0]

output:
  directory: "output"
  stl_name: "hammond_split_running.stl"

# Calibration - v4-only (v2/hammond_split.scad has no calibration render
# mode at all, unlike hammond.scad - see lib/hammond_split.py's
# CalibrationElement() docstring for the full derivation). vary_baseline
# shifts each of the 3 baseline ROWS by start+row*interval (not per-
# column - this machine has no per-column baseline_row/cutout_row sweep
# structure the way the cylinder family does). vary_cutout is accepted-
# but-ignored, same reason cutout_row above is a no-op.
calibration:
  test_char: "H"
  vary_baseline: false
  vary_cutout: false
  start: -0.7
  interval: 0.05

# The flat 2D "index" reference card - see config/hammond.yaml's matching
# comment/lib/hammond_legend.py's module docstring for what this is and
# where the numbers come from. Unlike hammond.yaml, there is no dedicated
# v1 "HammondSplitIndex.scad" (confirmed absent from v1/Hammond/ - Hammond
# Split's own module docstring already establishes it shares nothing else
# with plain Hammond either), so this reuses v1/Hammond/HammondIndex.
# scad's real numbers as a placeholder for the same 3-row/30-column
# shuttle-arc card shape - adjust qp_length_mm/z_exclamation_length_mm/
# center_to_center_height_mm here if Hammond Split's real physical
# shuttle dimensions differ.
legend:
  # Placeholder - reuses config/hammond.yaml's real hand-measured values
  # verbatim (see that config's matching comment) until Hammond Split's
  # own physically-different shuttle has its own real measurements taken;
  # not physically accurate for this machine yet.
  qp_length_mm: 178.0
  a_colon_length_mm: 188.0
  z_exclamation_length_mm: 198.0
  row_separation_mm: 18.45
  left_margin_mm: 38.0
  bottom_margin_mm: 9.2
  card_width_mm: 274.0
  card_height_mm: 60.0
  card_corner_radius_mm: 19.0
  card_corner_center_y_mm: 38.0
  card_border_stroke_mm: 0.1
  circle_id_mm: 14.0
  circle_thickness_mm: 0.5
  cap_size_mm: 6.0
  fig_size_mm: 4.0
  capfig_mod_size_mm: 4.0
  fig_offset_mm: 2.5
  lowercase_offset_mm: -5.5
  cap_offset_mm: -4.5
  fig_dupe_offset_mm: 3.0
  capfig_offset_mm: -1.5
  capfig_mod_chars: "!:?-\"&"
  # v1 Lowercase_Mod (see config/hammond.yaml's matching comment) plus
  # "?"/"."/ ":" - this config's own real layout.rows[0] (the lowercase
  # row) has these 3 as genuine standalone characters at their own key
  # (not the lowercase form of that key's own CAP letter - e.g. idx 0 is
  # "?" over CAP "!", not "!"'s lowercase form), so they'd otherwise be
  # silently dropped the same way Hammond's own dash was - see that
  # config's comment for the same reasoning/fix.
  lowercase_mod_chars: ";,'?.:"
  fig_dupe_chars: "."
  circle_segments: 32
  legend_flatness_tolerance_mm: 0.01
  background: "transparent"
  # v4-only, independent of font.path above - see config/hammond.yaml's
  # matching legend.legend_font_path comment (same shared HammondIndex.
  # scad legend design/font, "Franklin Gothic", and the same key-name
  # collision reasoning - this config's own label.font_path already owns
  # the bare font_path key text).
  legend_font_path: "/home/lchau/fonts/Library/Sans Text/Franklin Gothic.ttf"
