dairyking98/Type-Elements/v4/config/mignon.yaml

# Mignon type element - all real parameters ported 1:1 from
# v2/mignon.scad (see that file for authoritative source/comments).
# Mignon diverges from Blickensderfer/Postal's shared cylinder_machine.py
# across essentially the whole body-construction half of the pipeline -
# no wall/chamfer/speed-hole/core-groove/clip/drive-pin concepts at all,
# a 12-sided polygon main body instead of a round cylinder, a different
# top feature, a different shaft/alignment mechanism, and fully bespoke
# resin-support placement - so this file's element:/resin: sections are
# shaped very differently from theirs. See lib/mignon.py's module
# docstring for the full comparison. Only the glyph placement pipeline
# and the Calibration mechanism are genuinely shared - this file's
# layout:/calibration:/alignment: sections use the same schema as
# Blickensderfer/Postal's.

# generate.py/export_glyphs.py dispatch on this key to import
# blickensderfer.py/postal.py/mignon.py - see lib/cylinder_machine.py's
# docstring for the shared-module mechanism this feeds into.
machine: mignon

font:
  # v2's real value is the font family name "Iosevka Etoile" (Type_Size=
  # 2.45), not a file path - this is that font's real file.
  path: "/home/lchau/fonts/Library/Typewriter & Monospace/Iosevka Etoile.ttf"
  size_mm: 2.45

# Secondary font - characters listed in font2_chars are struck in this
# font/size instead of the main one. Same feature the Selectric family and
# Hammond Split have, under the same key names. Empty font2_chars =
# inactive (the default), so this changes nothing until it is filled in.
# The real use is glyph coverage: measured across the 170 distinct
# characters in all 28 Blickensderfer layout presets, Royal Vogue v3 is
# missing 87 (fractions, currency), Erica Type 52 (including "@"), Alma
# Mono and CMU Typewriter 50 each, and no non-Hebrew font covers the
# Hebrew-English preset at all.
font2:
  font2_path: ""            # blank = use the main font
  font2_size_mm: 0.0        # 0 = use the main font size
  font2_chars: ""

logo:
  # v2's real value is also "Iosevka Etoile" (Cylinder_Label_Font_Override
  # empty -> falls back to Typeface_). v2's own Cylinder_Label default
  # (Cylinder_Label_Override empty -> falls back to the FONT NAME STRING
  # itself, "Iosevka Etoile", as placeholder label text) isn't a
  # meaningful real value to port literally - using a real label instead,
  # matching Blickensderfer/Postal's own logo.text convention.
  font_path: "/home/lchau/fonts/Library/Typewriter & Monospace/Iosevka Etoile.ttf"
  text: "Leonard Chau 2026"
  # Cylinder_Label_Size_Override=0 -> 0.51*Type_Size = 0.51*2.45
  text_size_mm: 1.2495
  text_spacing: 15.0            # Cylinder_Label_Spacing (degrees between characters)
  position_offset_deg: 0.0      # Cylinder_Label_Offset
  # Cylinder_Label_Height_Offset - local radial nudge off the chamfer
  # surface ElementLabel() places the label on (see lib/mignon.py) - NOT
  # the same concept as Blickensderfer/Postal's radial_offset_mm (their
  # label sits flat on the top face; Mignon's sits on an angled chamfer
  # surface, a genuinely different placement geometry). 1.0/0.3 (not v2's
  # unmodified .5/.09) - see text_depth_mm below for why: at v2's thin
  # depth this offset alone leaves most of the text embedded/invisible.
  height_offset_mm: 1.0
  # v4-only, not a v2 field (v2 hardcodes .09) - how far the raised text
  # extends. The chamfer is a CURVED frustum and the text is a flat panel
  # resting tangent to it, so a thin extrusion only clears the surface at
  # the exact tangent point - increasing height_offset_mm alone just slides
  # the same thin sliver around rather than exposing the character, and
  # enough offset to clear the whole curve detaches it into a floating
  # island. A deeper extrusion spans embedded (anchored)->exposed
  # (visible) at a modest offset instead. Verified visually at 0.3/1.0:
  # full "Leonard Chau 2026" text solidly raised and attached all the way
  # around the arc, not just near center.
  text_depth_mm: 0.3
  # v4-only - v2 has no toggle, its small sphere-minkowski edge-rounding
  # is unconditional (gated only by the preview-quality Mink_On flag).
  # off (false): plain flat extrude, both Logo and Label text. on (true):
  # a real draft-cone taper (build.draft_angle_deg/quality.minkowski_fn -
  # the same knobs struck characters use), applied to BOTH Logo and
  # Label - one checkbox, not per-feature.
  minkowski_text: false

# v4-only second engraved-text feature (NOT a v2 concept - v2/mignon.scad
# has exactly one, Cylinder_Label, ported above as logo.*) - same
# font/size/spacing/height-offset format as logo above, always placed 180
# degrees opposite logo's position_offset_deg (derived in lib/mignon.py's
# configure(), not stored here - editing logo.position_offset_deg keeps
# the label locked opposite it). text defaults to empty (renders nothing)
# rather than duplicating logo.text verbatim - at logo's real 15deg/char
# spacing, "Leonard Chau 2026" (18 chars) already spans ~255 degrees, so a
# second copy of it 180 degrees away would heavily overlap the first
# rather than sitting cleanly opposite it. Fill in your own shorter text.
# Keys prefixed label_* (not font_path/text/... like logo above) - tune.py's
# patch_yaml_value matches by bare key text across the WHOLE config file,
# not by section, so identical key names under logo:/label: would collide
# (the same literal "font_path:"/"text:"/etc. appearing twice) and patch
# the wrong one - every YAML key patch_yaml_value can touch must be
# globally unique in the file (see GAUGE_FIELDS' matching comment in tune.py).
label:
  label_font_path: "/home/lchau/fonts/Library/Typewriter & Monospace/Iosevka Etoile.ttf"
  label_text: ""
  label_text_size_mm: 1.2495
  label_text_spacing: 15.0
  # see logo.height_offset_mm/text_depth_mm's matching comments above -
  # same curved-chamfer-vs-flat-panel reasoning applies here.
  label_height_offset_mm: 1.0
  label_text_depth_mm: 0.3

element:
  platen_diameter: 26.5
  element_diameter: 18.64
  min_final_character_diameter: 19.4
  # Cylinder_Height_=40.5 - the BASE/untallened height; actual built
  # Element_Height adds height_increase_mm on top of this when tallen is on.
  element_height: 40.5
  # Tallen (Plakatschrift, a display-type variant) - v2/mignon.scad:109-
  # 115,197. Off by default (matches v2's Tallen=false and this file's
  # real Layout_Selection=5 German 4 default, an untallened element).
  # When on: Element_Height = element_height + height_increase_mm, and
  # every baseline row shifts by tallen_baseline_offset_mm (cutout rows
  # are NOT affected - v2 has no Cutout_Tallen variant).
  tallen: false
  height_increase_mm: 3.0
  tallen_baseline_offset_mm: -1.25
  cylinder_top_height_offset: 3.0
  cylinder_top_chamfer: 2.0
  cylinder_top_diameter: 10.5
  cylinder_top_shaft_diameter: 7.3
  cylinder_bottom_shaft_diameter: 14.6
  pin_height: 1.8
  pin_width: 1.7
  pin_depth: 1.0
  pin_through: false
  cylinder_shape: 0    # 0=Polygonal (12-gon, v2 default), 1=Cylindrical

# quality/facet counts - Mignon's own naming (Cyl_Fn/Surface_Fn/Mink_Fn),
# no separate body_fn (PolygonCylinder has no circular facet count - it's
# already a flat N-gon) or groove_fn (no core grooves). Resin_Fn moved to
# resin.resin_fn below - Mignon used to be the sole quality.resin_fn
# outlier CLAUDE.md's "pick one convention" section documented by name;
# fixed to match the majority (Blickensderfer/Postal/Bennett/Hammond/
# Hammond Split/Selectric all use resin.resin_fn).
quality:
  cyl_fn: 360
  surface_fn: 360
  minkowski_fn: 12
  platen_fn: 360
  # Wall banding. The body is pre-split into horizontal bands so the boolean
  # that unions the characters into it never has a full-height face to
  # shatter into long near-zero-area slivers. Bands are never made SHORTER
  # than this; 0 = auto, one band per angular facet width (bands roughly as
  # tall as they are wide). Raise it to coarsen an over-fine wall.
  # Same case as Helios: auto wants 249 bands of 0.163mm here, which measured
  # identical to 20 bands of 2.025mm (worst sliver 5.415mm either way) while
  # costing 5276 extra faces.
  min_band_height_mm: 2.0

# per-row baseline/platen-cutout heights (mm, ABSOLUTE from the bottom
# face - v2/mignon.scad:281 Baseline_Z_Offset=0, unlike Blickensderfer/
# Postal's negative-from-clip-end convention), latitude spacing, and the
# physical layout (v2's German 4 / Layouts[5], the real default -
# Layout_Selection=5).
#
# rows: stored in RAW KEYBOARD-LEGEND order (v2's `Layout` array, matching
# what's printed on the physical keyboard/manual), NOT the Char_Legend-
# remapped `Physical_Layout` order used for actual glyph placement -
# mignon.py's configure() applies char_legend below to compute the real
# build-time DHIATENSOR, mirroring v2/mignon.scad:275's
# Physical_Layout=[for (row) [for (col) Layout[row][Char_Legend[col]]]]
# exactly. Mignon also has no separate placement_map override beyond
# Char_Legend - identity below.
layout:
  baseline_row: [2.25, 7.55, 12.75, 17.8, 22.8, 28.0, 32.8]
  cutout_row: [2.7, 8.25, 13.6, 18.7, 23.7, 28.7, 33.6]
  latitude_columns: 12
  placement_map: [0, 1, 2, 3, 4, 5, 6, 7, 8, 9, 10, 11]
  char_legend: [7, 8, 9, 10, 11, 0, 1, 2, 3, 4, 5, 6]
  rows:
    - "&():\"!?'äöü_"
    - "§PFUGQpfugq;"
    - "JVINABvinabj"
    - "/LDETMldetm,"
    - "%KOSRZkosrz="
    - "¾YCHWXychwx+"
    - "½¼23456789.-"
  modify_glyphs: false

alignment:
  mode: "center"
  center_offset_mm: 0.0
  left_offset_mm: 0.0
  modified_left_chars: ""
  modified_left_offset_mm: 0.0
  modified_right_chars: ""
  modified_right_offset_mm: 0.0
  # Per-character baseline overrides, y-axis counterparts to the
  # modified_left/right_chars nudges above (see glyph_poc.alignment_offset).
  # caret_drop_mm shifts "^" DOWN - the Blickensderfer's caret sits on the
  # baseline, but digital fonts draw U+005E up at cap height because there
  # it doubles as the spacing circumflex accent. underscore_lift_mm shifts
  # "_" UP - many TTFs sink U+005F well below the baseline to clear
  # descenders in running text, which drops it out of the character cell on
  # a struck element. Both 0.0 = use the font's own glyph position, i.e. the
  # behavior every config had before these keys existed. Idea/problem
  # statement from RobertG's OpenSCAD Blickensderfer generator
  # (badonoer.blogspot.com, CC BY-SA 4.0) caretDrop/uScoreLift.
  caret_drop_mm: 0.0
  underscore_lift_mm: 0.0

# mesh-pipeline build settings (v4-specific) + v2's Letter_Placement_
# Protrusion/Angle_Half_Step overrides (see cylinder_machine.
# place_on_cylinder's docstring) - Mignon's placement radius is the raw
# Element_Diameter/2 (no protrusion added at placement, unlike
# Blickensderfer/Postal) and has no half-column centering step.
build:
  flatness_tolerance_mm: 0.005
  pre_minkowski_char_height_mm: 1.0
  # MINKOWSKI CONE HEIGHT - the tapered part of the character, added BELOW
  # the straight part. Total character depth is pre_minkowski_char_height_mm +
  # this, and the tip does not move when either changes. Lower it for a
  # shallower flare without pulling the root out of the wall - which is
  # what shrinking the character alone used to do, until the roots lifted
  # clear and the characters floated free of the body.
  minkowski_cone_height_mm: 2.0
  # Trim each placed character to its own angular slot so its Minkowski
  # draft skirt cannot bleed into the neighbouring character. See
  # cylinder_machine._clip_to_cell. Off = the historical behavior.
  clip_to_cell: false
  resin_support: true
  target: "element"
  minkowski_enabled: true
  draft_angle_deg: 55.0
  placement_protrusion: 0.0
  angle_half_step: 0.0

# lib/resin_rod.scad only (Mignon includes just this, not
# lib/resin_support.scad's placement layer - see lib/mignon.py's
# ResinSupport(), fully bespoke). support_height/support_thickness are
# Mignon-specific (Resin_Support_Height/Resin_Support_Thickness), not
# part of Blickensderfer/Postal's resin: schema.
resin:
  resin_fn: 20
  rod_od: 1.0                 # Resin_Support_Wire_Thickness
  tip_od: 0.6                 # Resin_Support_Contact_Point_Diameter
  tip_l: 1.0
  inset: 0.0
  min_rod_height: 0.0
  raft_od: 1.0                # unused (Resin_Rod_Raft always false for Mignon), defined for clarity only
  raft_thickness: 0.0
  support_height: 4.0
  support_thickness: 2.0
  # v4-only - v2 hardcodes 12 evenly-spaced rods (v2/mignon.scad:341's
  # for(n=[0:11])) in both ResinSupport() and ResinSupportShaftEnd().
  # Increase to add more rods (both print orientations use this same
  # count); ResinSupport() (upside_down) also adds half this many more, on
  # alternating sectors, at a second radius near the top boss.
  rod_count: 12
  # [upside_down, right_side_up] - v4-only, no v2 equivalent. upside_down
  # (default) is v1/v2's original ResinPrint() flip (translate then
  # rotate([0,180,0]) - label end down at the build plate, see lib/
  # mignon.py's ResinPrint() docstring). right_side_up skips the flip: the
  # shaft/keyway end (AlignmentPin, CenterShaft bore) sits at the build
  # plate instead - see lib/mignon.py's ResinSupportShaftEnd().
  orientation: upside_down
  # Half-angle (degrees) around the AlignmentPin keyway (theta=0, see
  # AlignmentPin()) that ResinSupportShaftEnd() keeps clear of rod contact
  # points, placing a flanking pair at +/-notch_gap_deg instead of a rod
  # at 0 - same avoidance pattern spherical_machine.ResinRodAssemble()
  # uses around Selectric's Drive_Notch_Theta (its Tip_Notch_Offset). The
  # keyway itself spans about +/-6.2deg at the rod ring's radius
  # (atan((pin_width/2)/r1), r1=8.21mm) - 8.0 adds a small margin. Only
  # used when orientation is right_side_up.
  notch_gap_deg: 8.0

output:
  directory: "output"
  stl_name: "mignon_running.stl"

# tune.py's Type Test tab (v4-specific, not part of the real element or
# v2/mignon.scad) - see config/blickensderfer.yaml's matching comment.
type_test:
  cpi: 10.0
  lpi: 6.0
  text: |-
    to do: stop.
    wait! uh... no,
    (parentheses)
    excitement!

# Calibration (v2's Testing_Baseline/Testing_Cutout/Testing_Layout +
# Testing_Offsets, wired to the same Cutout_Test/Baseline_Test/Test_Layout
# mechanism Blickensderfer/Postal use) - see config/blickensderfer.yaml's
# matching comment. Mignon's real Testing_Offsets=[-.5,-.4,...,.6] (12
# columns) is exactly testSweepArray(-0.5, 0.1, 12).
calibration:
  test_char: "H"
  vary_baseline: false
  vary_cutout: true
  start: -0.5
  interval: 0.1

# The flat 2D "index" reference card - v1/Mignon/MignonIndex.scad ported
# to lib/mignon_legend.py (SVG output via generate_legend.py, entirely
# separate from the 3D element build above - see that module's
# docstring). Every number below is v1's real customizer default
# (MignonIndex.scad line cited), not invented. Displays layout.rows
# above (raw keyboard-legend order, not the char_legend-remapped
# DHIATENSOR the element itself is struck with).
legend:
  length_mm: 133.0             # v1 Length (:19, "Index Length")
  width_mm: 83.0                # v1 Width (:21, "Index Width")
  corner_radius_mm: 9.0         # v1 Corner_Radius (:37)
  edge_to_column_mm: 10.5       # v1 Edge_to_Column (:39)
  edge_to_row_mm: 9.5           # v1 Edge_to_Row (:41)
  circle_diameter_mm: 8.0       # v1 Circle_Diameter (:31)
  circle_height_bump_mm: 0.8    # v1 Circle_Height_Bump (:33) - Y-squish of every circle/ellipse
  line_width_mm: 0.3            # v1 Line_Width (:35) - ring/border stroke width
  square_pattern_size_mm: 0.5   # v1 Square_Pattern_Size (:43) - Checker only
  square_pattern_pitch_mm: 0.8  # v1 Square_Pattern_Pitch (:45) - Checker only
  # v1 Checker (:47) - the raw customizer DEFAULT is false ("slow - do
  # last"), but this is not what a real, finished card actually looks
  # like: MignonIndex.json's "New set 3" and its unnamed final preset
  # both match this config's own dimensions/layout exactly (Layout_
  # Selection=5, Length=133, Width=83) and both have Checker=true -
  # confirmed correct (not just visually similar) against a direct
  # openscad-nightly render, comparing actual SVG path vertex coordinates
  # point-by-point, not just a raster screenshot - an earlier raster/
  # crop-based comparison gave a false positive for a packing/density
  # bug that turned out not to be real once checked this way. See lib/
  # mignon_legend.py's _checker_pattern() docstring for the actual real
  # bug that WAS found and fixed alongside this (a corner-vs-center
  # rotation pivot).
  checker: true
  type_size_mm: 5.0             # v1 Type_Size (:51) - a paper/laser-cut card, unrelated to font.size_mm's 2.45mm engraved element size
  legend_height_offset_mm: 2.1         # v1 Height_Offset (:63) - circle center to text baseline
  circle_segments: 32           # v4-only - shapely buffer() quad_segs for every circle/ellipse (v1 used $fn=$preview?30:60, :79)
  # v1's Weight_Adj mechanism is unported (self-contradictory in v1, real
  # default value a no-op regardless) - see lib/mignon_legend.py's module
  # docstring. This replaces it: a plain outline buffer, positive=bolder,
  # negative=thinner, 0=v1's real default behavior.
  weight_adjustment_mm: 0.0
  # v1 LiningRectangle() (:260-267) - real geometry, but dead code in
  # v1's own actual output (only Array1() calls it, and Array1() itself
  # is never invoked - see lib/mignon_legend.py's module docstring).
  # Off by default (matching v1's real behavior of never drawing it) -
  # turn on for an explicit border around the interior circle grid.
  inner_border: false
  # v4-only, not a v1 concept - SVG canvas background: "transparent"
  # (default, no backing rect) or "white" (an opaque backing rect, e.g.
  # for viewers/pipelines that composite onto a dark background and
  # would otherwise show every checker/circle hole as see-through).
  background: "transparent"
  # v4-only, independent of font.path above - the legend is a laser-cut/
  # printed paper card, not the 3D engraved element, so there's no reason
  # it has to share that typeface. v1's real value is the font family
  # name "Consolas" (MignonIndex.scad's Typeface_) - now installed here.
  # Named legend_font_path, not bare font_path - the Logo tab's own
  # logo.font_path already owns that literal key text (tune.py's
  # patch_yaml_value matches by bare key across the whole file, not by
  # section).
  legend_font_path: "/home/lchau/fonts/Library/Typewriter & Monospace/Consolas.ttf"
  # v1 Character_Modifieds/Character_Modifieds_Offset (:61-72) - per-
  # character baseline nudge groups. Offsets default to 0.0 here, NOT
  # v1's customizer-comment values (1.0/0.4/0.4/-0.5) - confirmed via a
  # real openscad-nightly render that v1's own indexing bug
  # (MignonIndex.scad:464 - see lib/mignon_legend.py's module docstring)
  # makes this a no-op in v1's actual output. The mechanism itself works
  # correctly here (unlike v1) - raise these above 0.0 to really use it.
  height_offset_groups:
    underscore_chars: "_"
    underscore_offset_mm: 0.0
    descender_chars: "pgqjy"
    descender_offset_mm: 0.0
    parenthesis_chars: "()"
    parenthesis_offset_mm: 0.0
    ascender_chars: "fbldtkh"
    ascender_offset_mm: 0.0
  # v1 NormalCircleFillArray/NormalBackgroundFillArray/NormalSolidFillAray
  # (:126-151) - only the Normal* arrays: v1's own Plakat* variants of
  # these 3 arrays (:96-123) are dead code, never assigned to
  # CircleFillArray/BackgroundFillArray/SolidFillArray anywhere in the
  # file (only the Normal* arrays are, unconditionally, at :155-157) -
  # not ported. 7 rows x 12 cols, same grid layout.rows uses above.
  circle_fill:      # 1 = a solid dark disc with the character cut OUT as a hole (reads as reversed/light-on-dark once filled - see mignon_legend.render_svg())
    - [0,0,0,0,0,0,0,0,0,0,0,0]
    - [0,1,1,1,1,1,0,0,0,0,0,0]
    - [0,1,1,1,1,1,0,0,0,0,0,0]
    - [0,1,1,1,1,1,0,0,0,0,0,0]
    - [0,1,1,1,1,1,0,0,0,0,0,0]
    - [0,1,1,1,1,1,0,0,0,0,0,0]
    - [0,0,0,0,0,0,0,0,0,0,0,0]
  background_fill:  # 0 = cut away entirely (leaves the border frame + isolated circles standing)
    - [1,1,1,1,1,1,1,1,1,1,1,1]
    - [1,0,0,0,0,0,0,0,0,0,0,1]
    - [1,0,0,0,0,0,0,0,0,0,0,1]
    - [1,0,0,0,0,0,0,0,0,0,0,1]
    - [1,0,0,0,0,0,0,0,0,0,0,1]
    - [1,0,0,0,0,0,0,0,0,0,0,1]
    - [1,1,1,1,1,1,1,1,1,1,1,1]
  solid_fill:       # 1 = a solid background square (with the same circle cut through it) behind an outlined-ring cell
    - [0,0,0,0,0,0,0,0,0,0,0,0]
    - [0,0,0,0,0,0,1,1,1,1,1,0]
    - [0,0,0,0,0,0,1,1,1,1,1,0]
    - [0,0,0,0,0,0,1,1,1,1,1,0]
    - [0,0,0,0,0,0,1,1,1,1,1,0]
    - [0,0,0,0,0,0,1,1,1,1,1,0]
    - [0,0,0,0,0,0,0,0,0,0,0,0]
  legend_flatness_tolerance_mm: 0.01   # adaptive glyph-outline tolerance (see glyph_poc.py) - a paper legend needs far less precision than a struck element
